flinguenheld/chew/images/hen.png

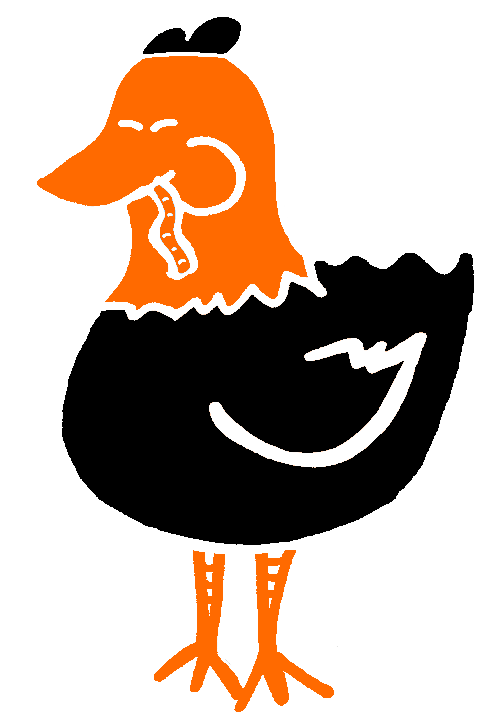
images/hen.png
