flinguenheld/chew/images/prawn_large.png

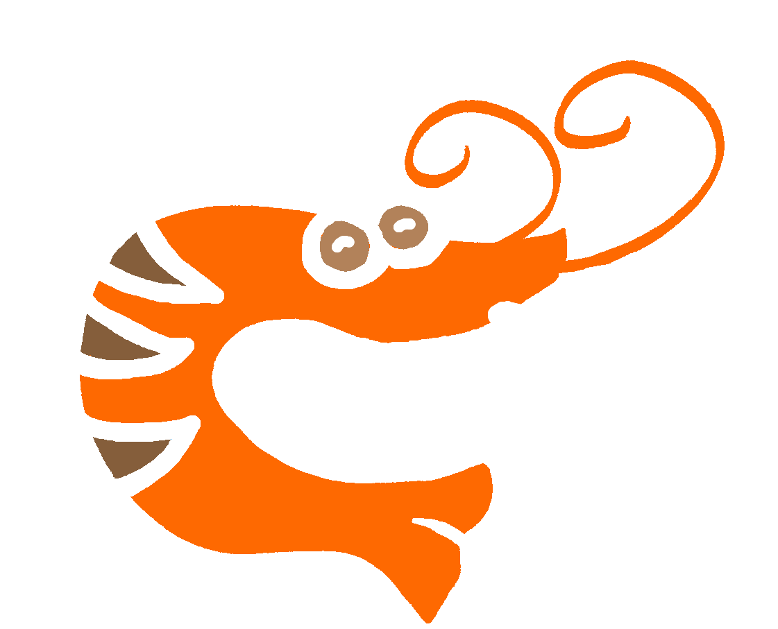
images/prawn_large.png
