flinguenheld/chew/images/rabbit.png

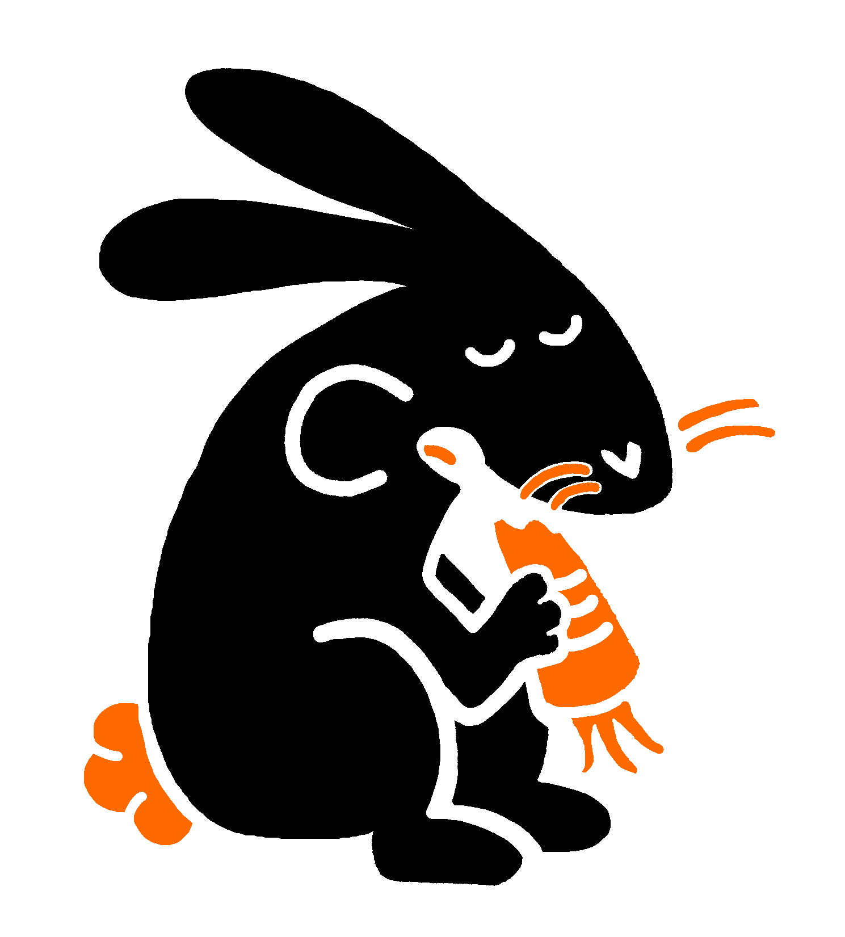
images/rabbit.png
