flinguenheld/chew/kicad/art/bar.png

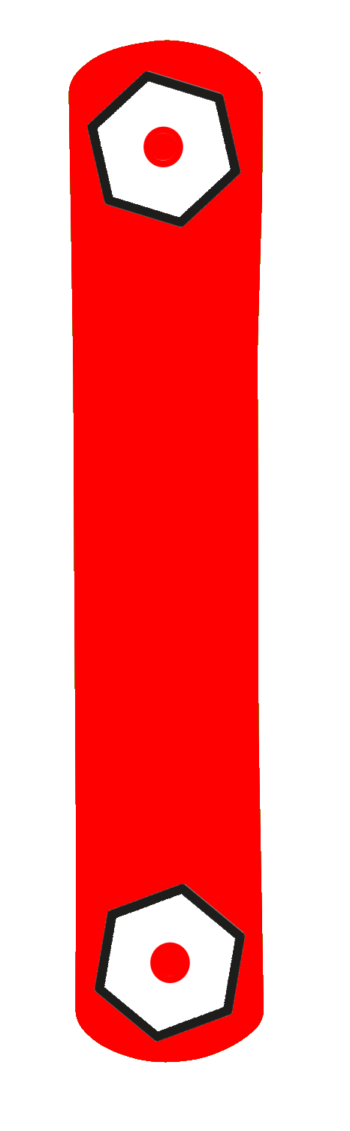
kicad/art/bar.png
