flinguenheld/chew/kicad/art/bar_2.png

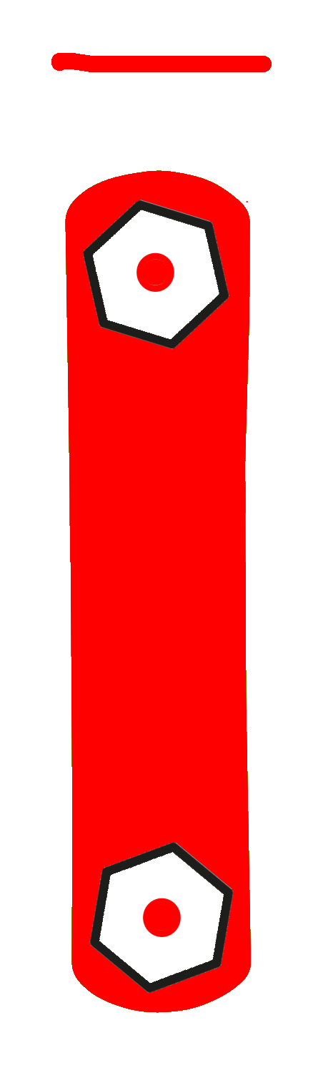
kicad/art/bar_2.png
