flinguenheld/chew/kicad/art/carrot_1.png

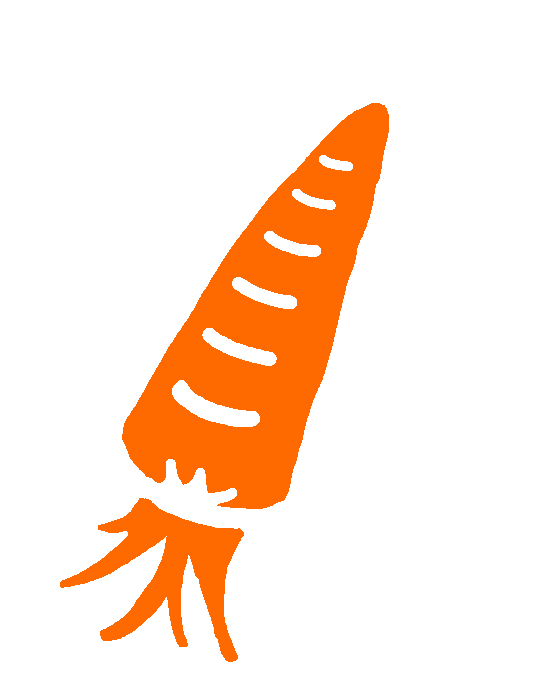
kicad/art/carrot_1.png
