flinguenheld/chew/kicad/art/carrot_2.png

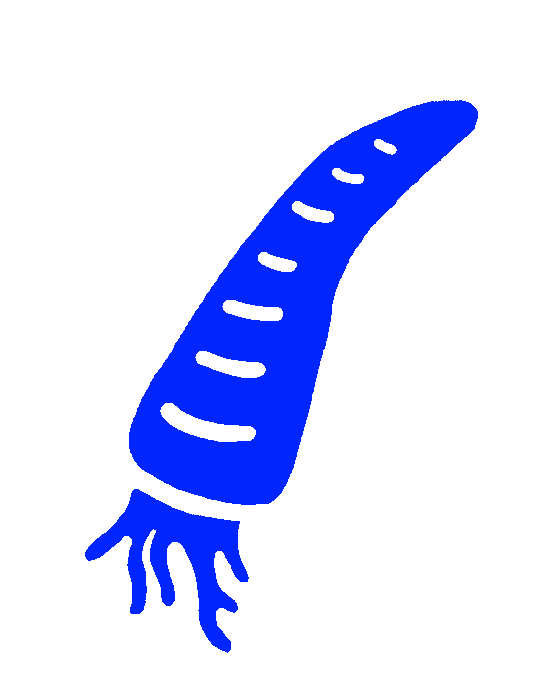
kicad/art/carrot_2.png
