flinguenheld/chew/kicad/art/carrot_3.png

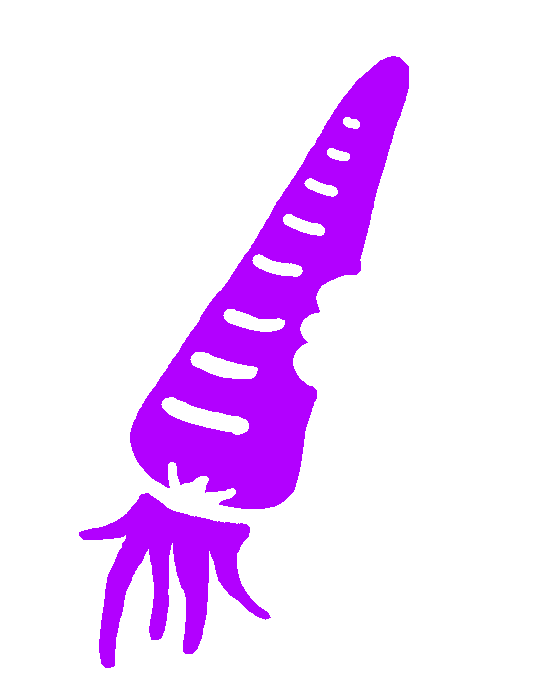
kicad/art/carrot_3.png
