flinguenheld/chew/kicad/art/chew_1.png

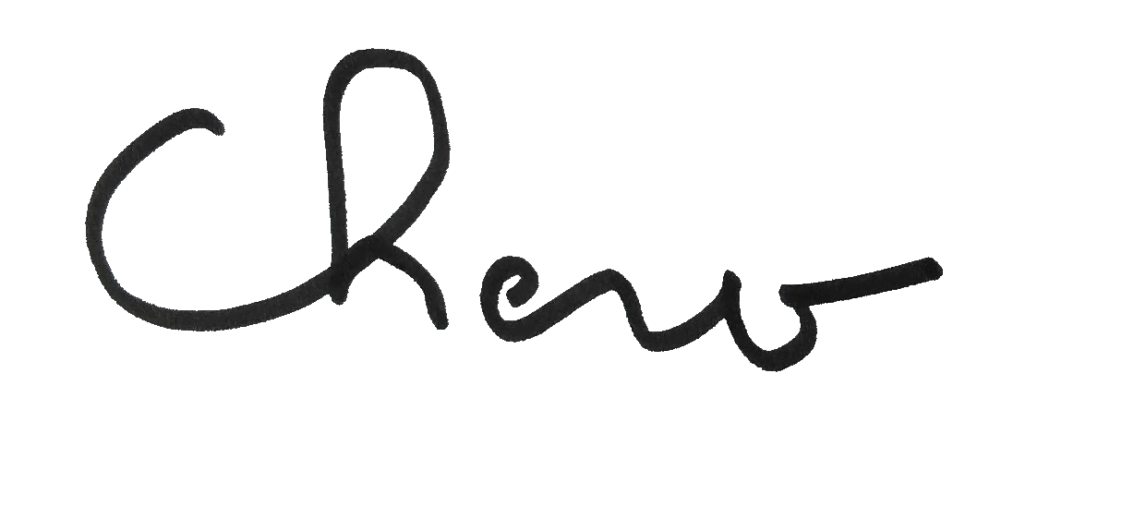
kicad/art/chew_1.png
