flinguenheld/chew/kicad/art/chew_2.png

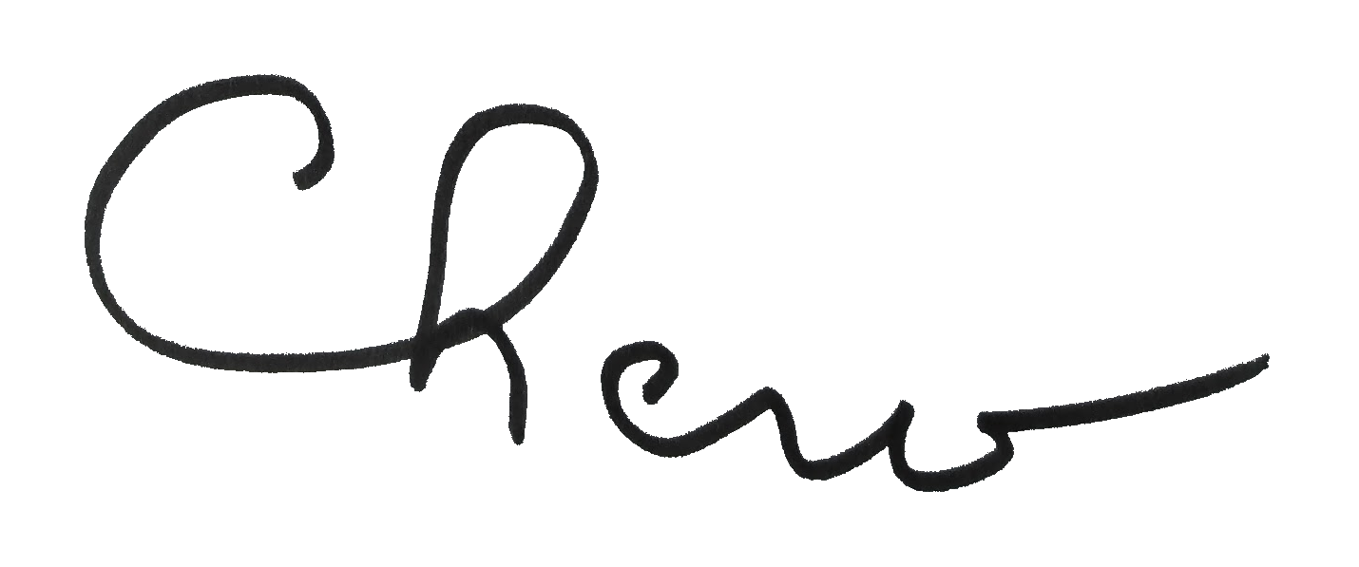
kicad/art/chew_2.png
