flinguenheld/chew/kicad/art/hazelnut.png

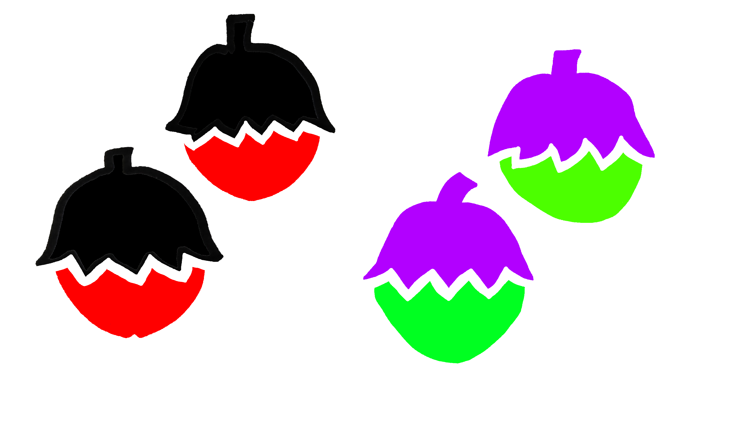
kicad/art/hazelnut.png
