flinguenheld/chew/kicad/art/hedgedog.png

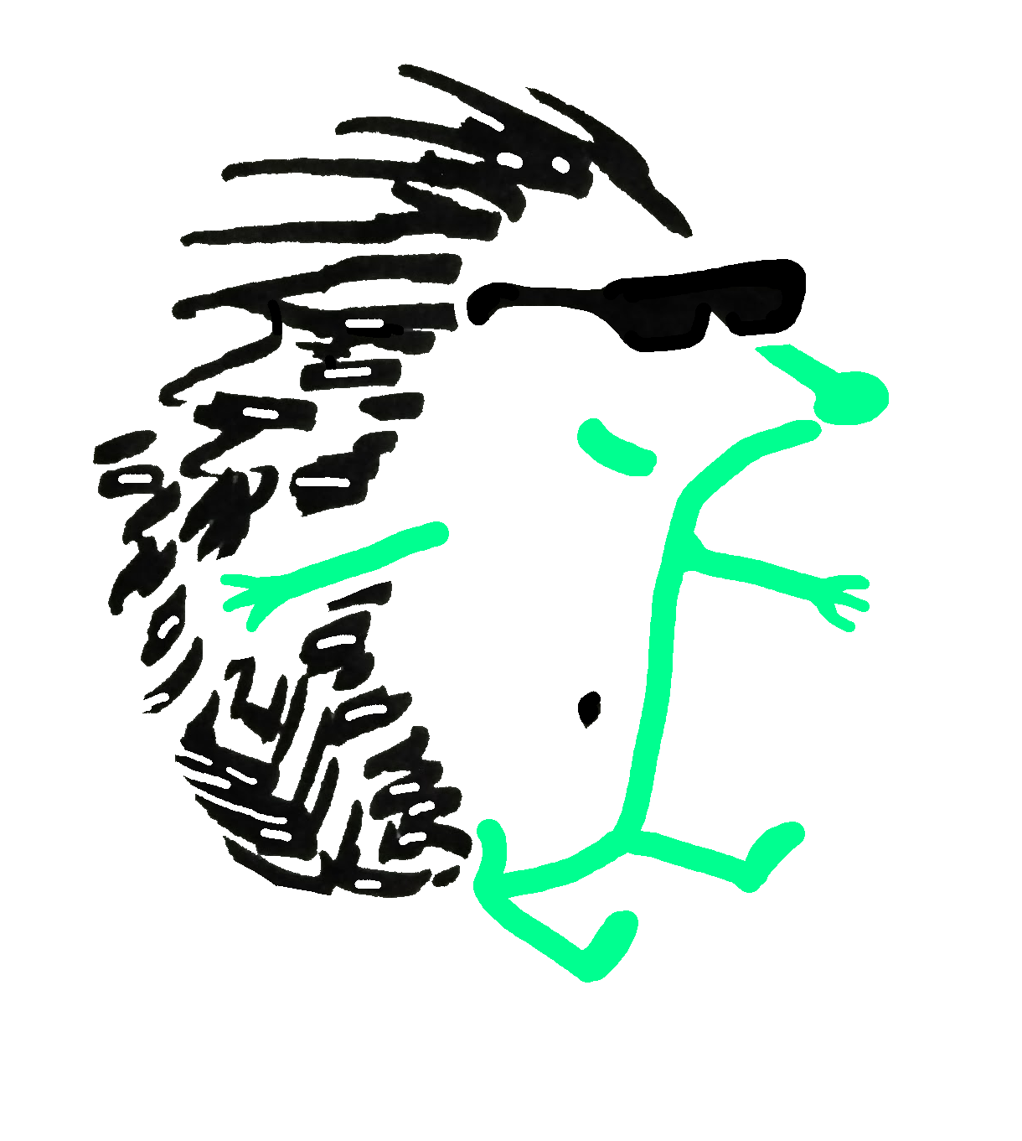
kicad/art/hedgedog.png
