flinguenheld/chew/kicad/art/high_squirrel.png

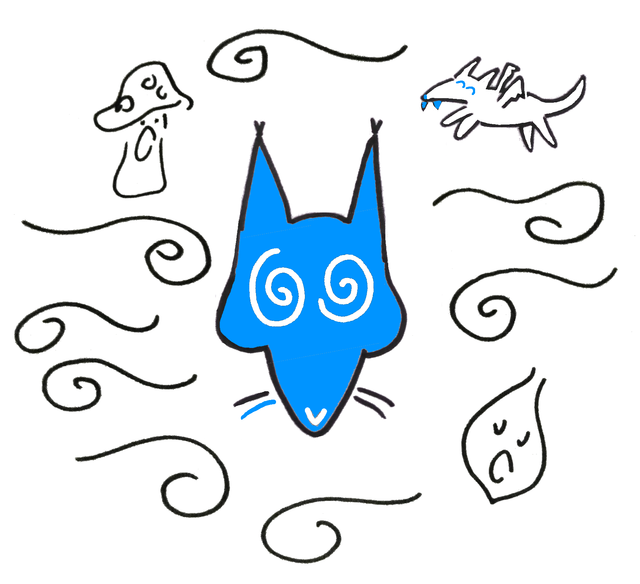
kicad/art/high_squirrel.png
