flinguenheld/chew/kicad/art/mouse.png

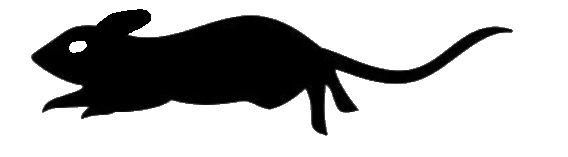
kicad/art/mouse.png
