flinguenheld/chew/kicad/art/mushroom.png

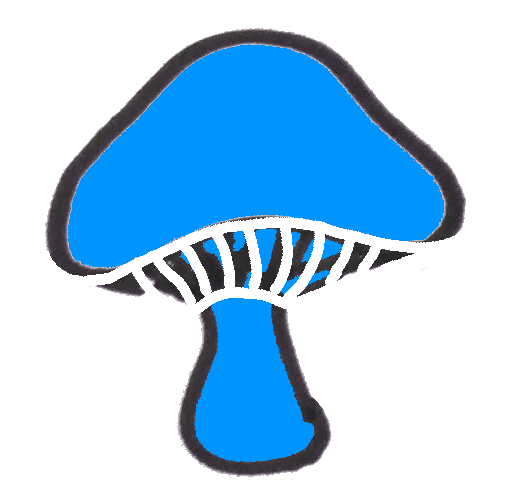
kicad/art/mushroom.png
