flinguenheld/chew/kicad/art/rabbit.png

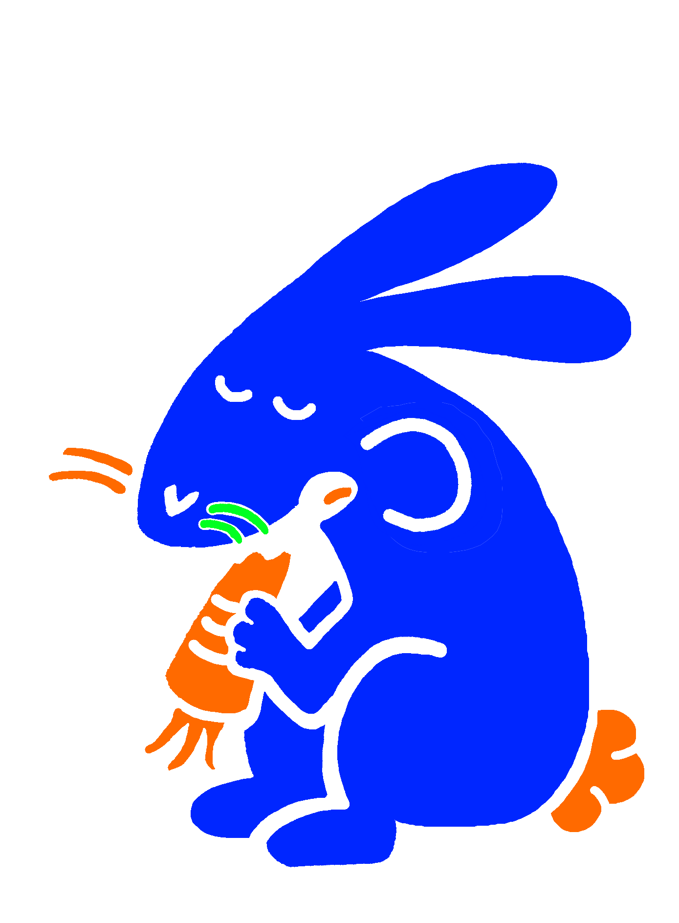
kicad/art/rabbit.png
