flinguenheld/chew/kicad/art/radish.png

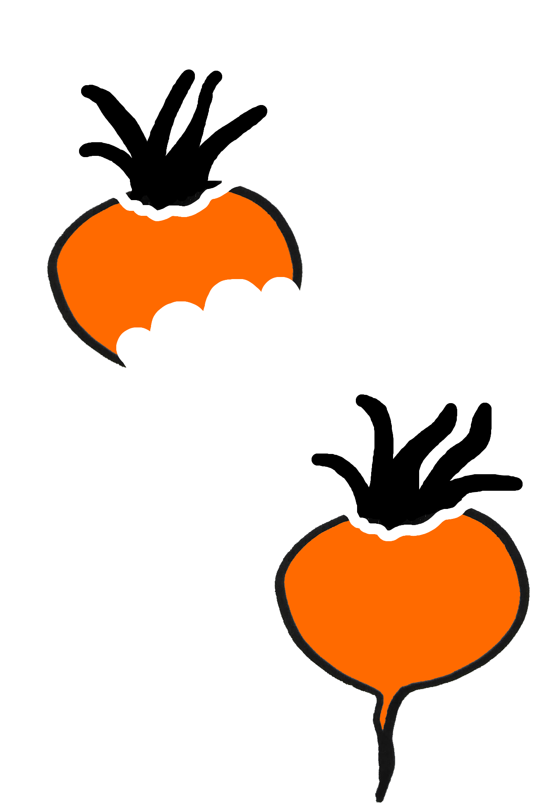
kicad/art/radish.png
