flinguenheld/chew/kicad/art/squirrel.png

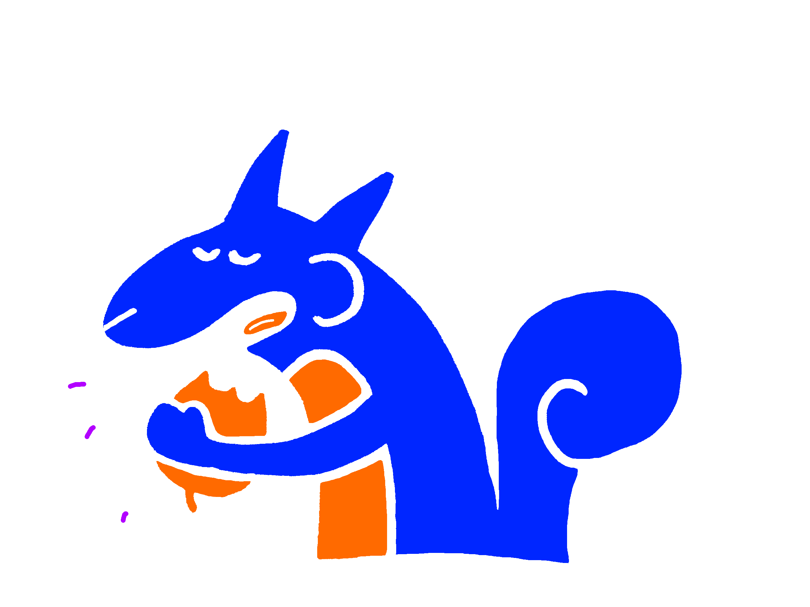
kicad/art/squirrel.png
