flinguenheld/chew/kicad/art/walnut.png

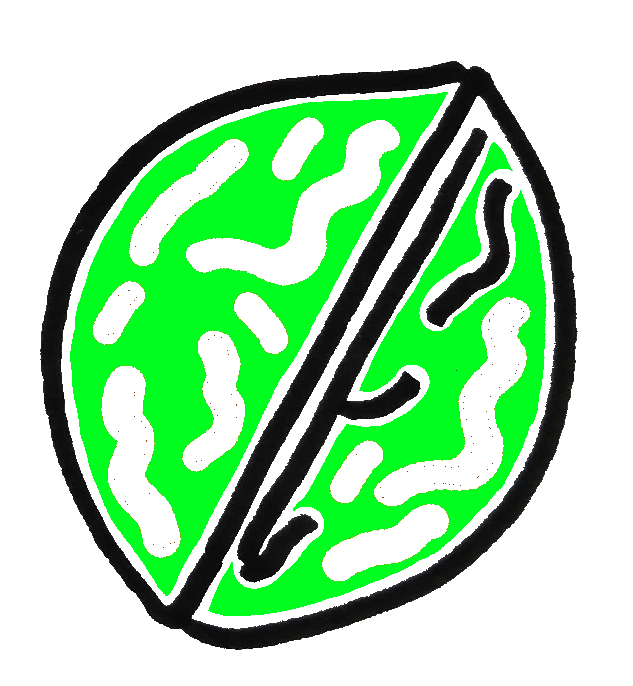
kicad/art/walnut.png
