flinguenheld/chew/kicad/art/wolf.png

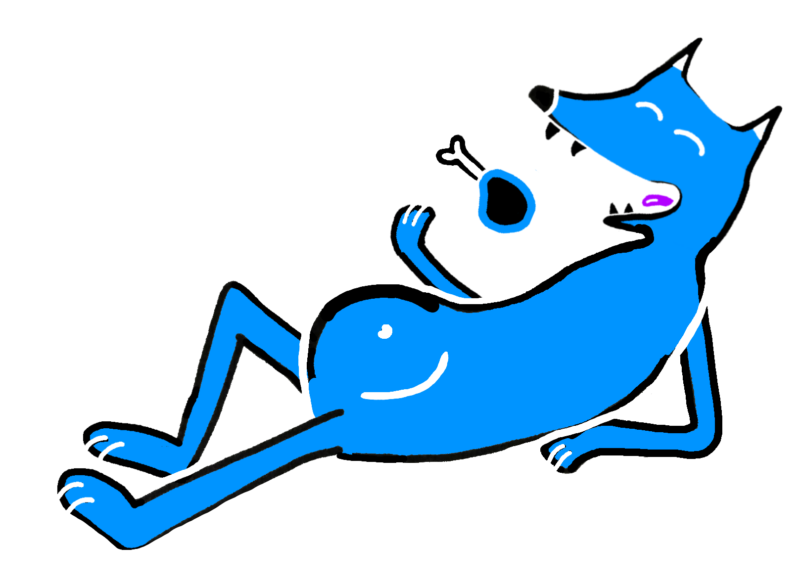
kicad/art/wolf.png
