flinguenheld/chew/kicad/art/wolf_plate.png

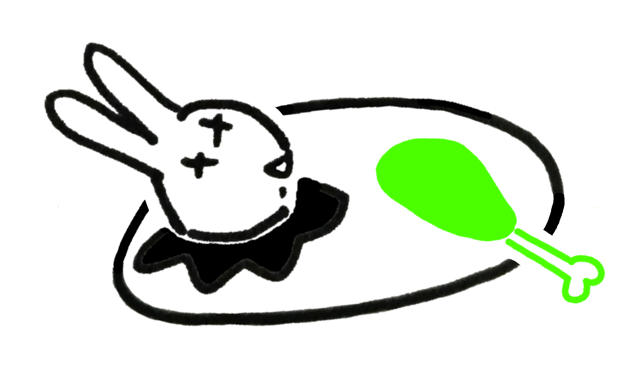
kicad/art/wolf_plate.png
