flinguenheld/chew/kicad/art/wolf_rabbit.png

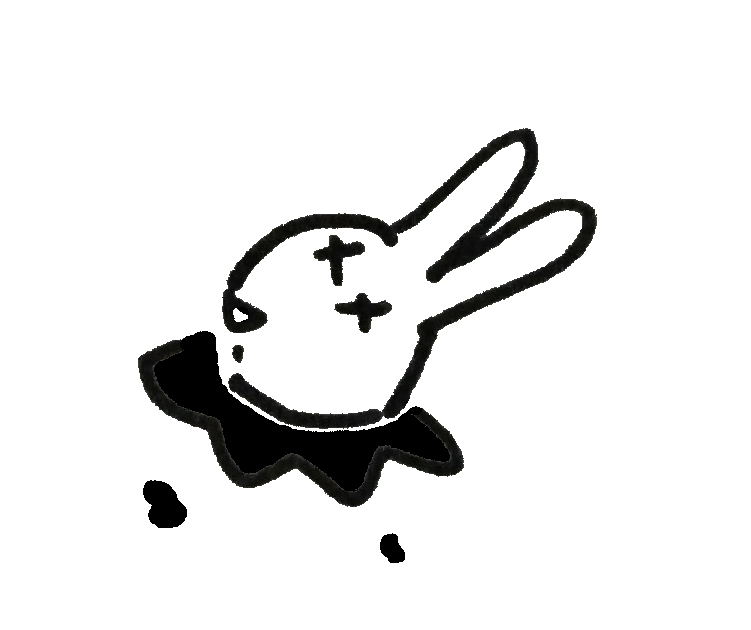
kicad/art/wolf_rabbit.png
