flinguenheld/chew/images/sausages_2.png

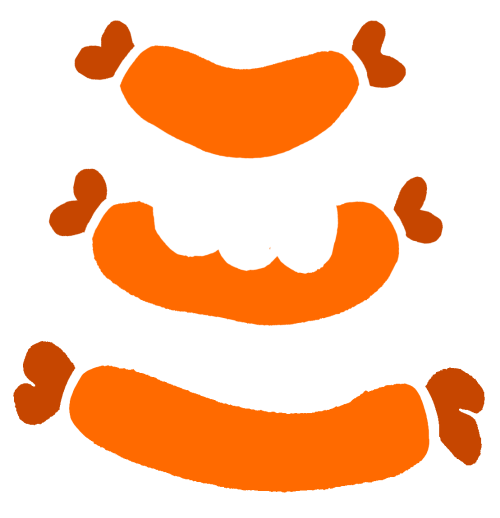
images/sausages_2.png
