flinguenheld/chew/routes/routes.kicad_sch

## KiCad design routes/routes.kicad_sch (2024-03-05)

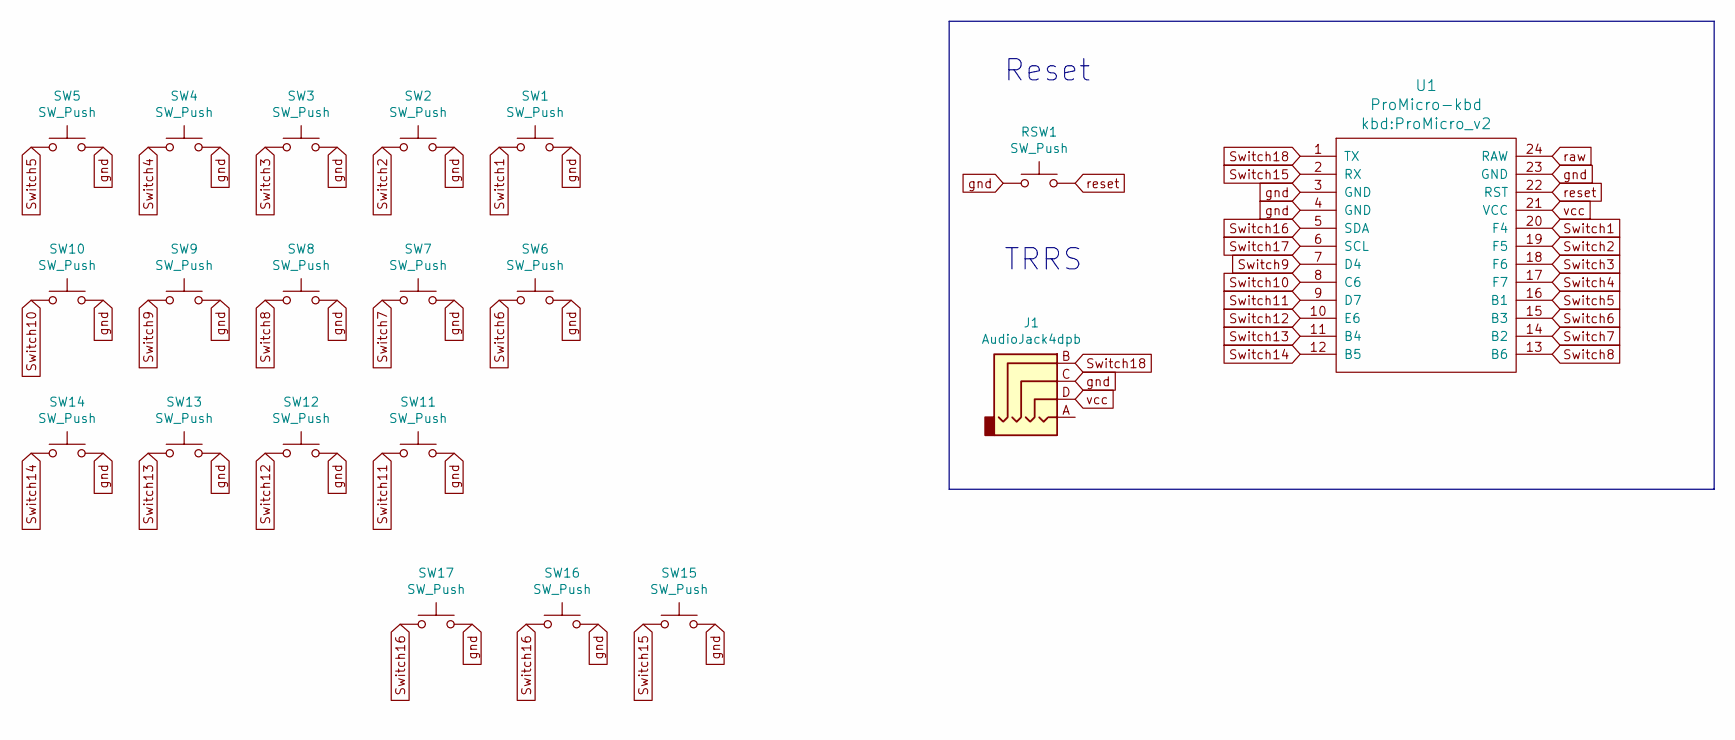
[picture p38: schematic routes.kicad_sch]

Parts:
J1: AudioJack4dpb; MJ-4PP-9
RSW1: SW_Push; ResetSW
SW1, SW2, SW3, SW4, SW5, SW6, SW7, SW8, SW9, SW10, SW11, SW12, SW13, SW14, SW15, SW16, SW17: SW_Push; SW_PG1350_rev_DPB
U1: ProMicro-kbd; ProMicro_v2

Connections:
Switch1: SW1.1, U1.20 (F4)
Switch2: SW2.1, U1.19 (F5)
Switch3: SW3.1, U1.18 (F6)
Switch4: SW4.1, U1.17 (F7)
Switch5: SW5.1, U1.16 (B1)
Switch6: SW6.1, U1.15 (B3)
Switch7: SW7.1, U1.14 (B2)
Switch8: SW8.1, U1.13 (B6)
Switch9: SW9.1, U1.7 (D4)
Switch10: SW10.1, U1.8 (C6)
Switch11: SW11.1, U1.9 (D7)
Switch12: SW12.1, U1.10 (E6)
Switch13: SW13.1, U1.11 (B4)
Switch14: SW14.1, U1.12 (B5)
Switch15: SW15.1, U1.2 (RX)
Switch16: SW16.1, SW17.1, U1.5 (SDA)
Switch17: U1.6 (SCL)
Switch18: J1.B, U1.1 (TX)
gnd: J1.C, RSW1.1, SW1.2, SW2.2, SW3.2, SW4.2, SW5.2, SW6.2, SW7.2, SW8.2, SW9.2, SW10.2, SW11.2, SW12.2, SW13.2, SW14.2, SW15.2, SW16.2, SW17.2, U1.3 (GND), U1.4 (GND), U1.23 (GND)
raw: U1.24 (RAW)
reset: RSW1.2, U1.22 (RST)
vcc: J1.D, U1.21 (VCC)

Notes on the sheet:
TRRS
Reset
